mincrmatt12/MSynth/bootloader/src/boot.c

#include "boot.h"
#include <stm32f4xx.h>
#include <core_cm4.h>
#include "stm32f4xx_ll_bus.h"
#include "sys.h"
#include "ui.h"

void boot_app(const app_hdr *app) {
	// TODO: load the BKP data correctly
	
	// Disable all interrupts
	RCC->CIR = 0;

	// Setup VTOR
	SCB->VTOR = app->vectab;

	RCC->APB1RSTR |= RCC_APB1RSTR_USART3RST | RCC_AHB1RSTR_GPIODRST | RCC_AHB1RSTR_GPIOFRST;
	asm volatile ("nop");
	asm volatile ("nop");
	asm volatile ("nop");
	asm volatile ("nop");
	asm volatile ("nop");
	asm volatile ("nop");
	asm volatile ("nop");
	asm volatile ("nop");
	asm volatile ("nop");
	asm volatile ("nop");
	asm volatile ("nop");
	asm volatile ("nop");
	RCC->APB1RSTR &= ~(RCC_APB1RSTR_USART3RST | RCC_AHB1RSTR_GPIODRST | RCC_AHB1RSTR_GPIOFRST);
	
	uint32_t topofstack = app->topofstack;
	uint32_t entry      = app->entry;

	// Load the important information into registers r0-r1
	asm volatile (
		"msr msp, %[TopOfStack]\n\t"
		"ldr lr, =app_return_handler\n\t"
		"bx %[StartAddr]\n\t"
		:: [TopOfStack]"r"(topofstack), [StartAddr]"r"(entry)
	);
	
	// The app returned; it shouldn't since we set the
	// return address to something different by messing with the stack.
	//
	// This causes the app to jump to a specific handler, which is capable of
	// parsing the data contained within the bootcmd struct and/or restarting
	// cleanly in case of error. It also supports invoking the debug handlers.
	//
	// It should _not_ call reset.
	
	// TEMP: spin
	// no msg, since USART3 may have been reconfigured
	while (1) {;}
}

void __attribute__((naked)) app_return_handler() {
	asm volatile (
		"mov r2, r0\n\t"           // Save the return value
		"ldr r0, =0x08000000\n\t"  // Load our initial stack value (almost certainly the top of CCMRAM)
		"ldr r0, [r0]\n\t"         // *(0x0800 0000)
		"msr msp, r0\n\t"          // set that stack
		"ldr r1, =app_return_handler_impl\n\t"  // app_return_handler_impl(), now with a sane stack
		"mov r0, r2\n\t"           // Pass the original return to this function
		"bx r1\n\t"
	);
}

extern int _write(int, const char *, int);

void __attribute__((noreturn)) app_return_handler_impl(uint32_t return_from_func) {
	// rerun sys-init
	sys_init();
	// directly _write (since we don't re-init libc)
	_write(0, "app returned\n", 13);
	// in future, setup bootcmd
	while(1) {;}
}
